Strilanc/Hand-Qubits/quball/test/test.cpp

#include "ArduinoTestHarness.h"
#include "TestUtils.h"
#include <string>
#include <stdio.h>
#include <exception>

static std::string cur_name = "";
static int cur_assert = 0;
void harness_main();
void quaternion_main();
void contact_main();
void motion_main();

int main() {
    harness_main();
    quaternion_main();
    contact_main();
    motion_main();
    printf("ALL PASS\n");
	return 0;
}

void test_without_reset(std::string name, void(*func)(void)) {
    cur_assert = 0;
    cur_name = name;
    func();
}

void test(std::string name, void(*func)(void)) {
    test_harness_reset_arduino_state();
    cur_assert = 0;
	cur_name = name;
	func();
}

void assert(bool truth) {
	cur_assert++;
	if (!truth) {
		throw "assert in " + cur_name + " at #" + std::to_string(cur_assert);
	}
}
